dahamif/Analog-Stomp-box-Guitar-Pedals/simulation files/Wah.asc

C1: cap; 10n
C2: cap; 10n
C3: cap; 10µ
C4: cap; 10µ
R1-v: res; 10k
R1: res; 80K
R2-v: res; 10k
R2: res; 0
R3: res; 160K
R4: res; 500
U2: TL072
V1: voltage; SINE(0 0.132 1k)
V2: voltage; 9
Named nets: Output, 0, +4.5, -4.5, Input
.tran 10ms
