dahamif/Analog-Stomp-box-Guitar-Pedals/simulation files/Distortion.asc

C1: cap; 100µ; V=6.3 Irms=0 Rser=0 Lser=0 mfg="Murata" pn="GRM21BR60J107ME15" type="X5R"
C2: cap; 47µ; V=2.5 Irms=0 Rser=0 Lser=0 mfg="Murata" pn="GRM188R60E476ME15" type="X5R"
C3: cap; 0.047µ; V=4 Irms=760m Rser=0.0732706 Lser=0 mfg="KEMET" pn="C0402C473K7PAC" type="X5R"
C4: cap; 0.47µ; V=4 Irms=3.38 Rser=0.0190129 Lser=0 mfg="KEMET" pn="C0805C474K7PAC" type="X5R"
C5: cap; 0.047µ; V=4 Irms=760m Rser=0.0732706 Lser=0 mfg="KEMET" pn="C0402C473K7PAC" type="X5R"
C6: cap; 240p; V=50 Irms=0 Rser=0 Lser=0 mfg="Murata" pn="GCM1555C1H241JA16" type="C0G"
C7: cap; 0.068µ; V=4 Irms=1.1 Rser=0.0536347 Lser=0 mfg="KEMET" pn="C0402C683K7PAC" type="X5R"
C8: cap; 100p; V=10 Irms=0 Rser=0.8826 Lser=319p mfg="Würth Elektronik" pn="885012207004 WCAP-CSGP 0805" type="X7R"
C9: cap; 0.47µ; V=4 Irms=3.38 Rser=0.0190129 Lser=0 mfg="KEMET" pn="C0805C474K7PAC" type="X5R"
C10: cap; 0.47µ; V=4 Irms=3.38 Rser=0.0190129 Lser=0 mfg="KEMET" pn="C0805C474K7PAC" type="X5R"
C11: cap; 0.01µ; V=4 Irms=162m Rser=0.395426 Lser=0 mfg="KEMET" pn="C0402C103K7PAC" type="X5R"
C12: cap; 0.022µ; V=4 Irms=356m Rser=0.150334 Lser=0 mfg="KEMET" pn="C0402C223K7PAC" type="X5R"
C13: cap; 0.1µ; V=4 Irms=0 Rser=0 Lser=0 mfg="Murata" pn="GRM022R60G153KE15" type="X5R"
C14: cap; 0.047µ; V=4 Irms=760m Rser=0.0732706 Lser=0 mfg="KEMET" pn="C0402C473K7PAC" type="X5R"
C15: cap; 1µ; V=4 Irms=0 Rser=0 Lser=0 mfg="Murata" pn="GRM032R60G105ME05" type="X5R"
D1: diode; 1N914
D2: diode; 1N4148
D3: diode; 1N4148
D4: diode; 1N4148
Q1: npn; 2SC2240
Q2: npn; 2SC2240
Q3: npn; 2SC2240
R1: res; 10k
R2: res; 10k
R3: res; 1K; tol=1 pwr=0.1
R4: res; 470k
R5: res; 10k
R6: res; 100K; tol=1 pwr=0.1
R7: res; 100k
R8: res; 470k
R9: res; 10K; tol=1 pwr=0.1
R10: res; 22
R11: res; 100K; tol=1 pwr=0.1
R12: res; 47.5K; tol=1 pwr=0.1
R13: res; 100K; tol=1 pwr=0.1
R14: res; 4.75K; tol=1 pwr=0.1
R15: res; 2.21K; tol=1 pwr=0.1
R16: res; 2.21K; tol=1 pwr=0.1
R17: res; 6.81K; tol=1 pwr=0.1
R18: res; 6.81K; tol=1 pwr=0.1
R19: res; 10k
R20: res; 1Meg; tol=1 pwr=0.1
R21: res; 1Meg; tol=1 pwr=0.1
R22: res; 10K; tol=1 pwr=0.1
R23: res; 1K; tol=1 pwr=0.1
R24: res; 100K; tol=1 pwr=0.1
R25: res; 50k
R26: res; 50k
R27: res; 10k
R28: res; 10k
R29: res; 50k
R30: res; 50k
U1: TL072
U2: TL072
V1: voltage; SINE(0 0.132 1k); AC 1
V2: voltage; 9
Named nets: +9V, +4.5V, 0, INPUT, Output
.tran 10ms
