dahamif/Analog-Stomp-box-Guitar-Pedals/simulation files/Phaser.asc

C1: cap; 47n
C2: cap; 10n
C3: cap; 47n
C4: cap; 47n
C5: cap; 47n
C6: cap; 0.01µ
C7: cap; 15µ
C10: cap; 47nF
D1: zener; 1N750
J1: njf; MPF102
J2: njf; MPF102
J3: njf; MPF102
J4: njf; MPF102
Q1: pnp; BC640
R1: res; 22k
R2: res; 10k
R3: res; 24k
R4: res; 10k
R5: res; 12.5k
R6: res; 470k
R7: res; 10k
R8: res; 470k
R9: res; 22k
R10: res; 10k
R11: res; 24k
R12: res; 22k
R13: res; 10k
R14: res; 24k
R15: res; 22k
R16: res; 10k
R17: res; 24k
R18: res; 150k
R19: res; 150k
R20: res; 3.9Meg
R21: res; 200k
R22: res; 270k
R26: res; 150k
R27: res; 150k
R28: res; 150k
R29: res; 56k
R30: res; 150k
U1: TL072
U2: TL072
U3: TL072
U4: TL072
U5: TL072
U6: TL072
V1: voltage; SINE(0 0.132 256); AC 1
V2: voltage; 9
Named nets: 0, Input, +4.5V, +9V, Output
.tran 100ms
